myelin/arcflash/os_switcher_bootloader/display.cc

// Copyright 2019 Google LLC
//
// Licensed under the Apache License, Version 2.0 (the "License");
// you may not use this file except in compliance with the License.
// You may obtain a copy of the License at
//
//     http://www.apache.org/licenses/LICENSE-2.0
//
// Unless required by applicable law or agreed to in writing, software
// distributed under the License is distributed on an "AS IS" BASIS,
// WITHOUT WARRANTIES OR CONDITIONS OF ANY KIND, either express or implied.
// See the License for the specific language governing permissions and
// limitations under the License.

#include "arcflash.h"
#include <stdarg.h>

int display_x = 0, display_y = 0;

// riscosfont is defined in third_party/riscos/riscos_font.s
extern "C" {
	extern const uint8_t riscos_font[8 * 256];
}

void display_goto(int x, int y) {
	display_x = x;
	display_y = y;
}

static void newline() {
	display_x = 0;
	display_y += 8;
	if (display_y > HEIGHT - 1) {
		// copy entire page up 8 rows
		for (volatile uint32_t *ptr = (volatile uint32_t *)SCREEN;
			ptr < (volatile uint32_t *)SCREEN_ADDR(0, HEIGHT - 8);
			ptr++)
		{
			*ptr = *(volatile uint32_t *)((volatile uint8_t *)ptr + WIDTH * 8);
		}
		display_y -= 8;

		// clear bottom row
		for (volatile uint32_t *ptr = (volatile uint32_t *)SCREEN_ADDR(0, HEIGHT - 8);
			ptr < (volatile uint32_t *)SCREEN_ADDR(0, HEIGHT);
			ptr++)
		{
			*ptr = 0;
		}
	}
}

void display_print_char(char c) {
	switch (c) {
		case '\r':
			display_x = 0;
			return;
		case '\n':
			newline();
			return;
	}

	const uint8_t *patternptr = &riscos_font[8 * c];
	volatile uint8_t *displayptr = SCREEN + display_x + display_y * 640;
	for (int y = 0; y < 8; ++y) {
		uint8_t pattern = *patternptr++;
		for (int x = 0; x < 8; ++x) {
			SCREEN[(y + display_y) * WIDTH + (x + display_x)] = (pattern & 0x80) ? WHITE : BLACK;
			pattern <<= 1;
		}
		displayptr += 640 - 8;
	}
	display_x += 8;
	if (display_x >= WIDTH) {
		newline();
	}
}

void display_print(const char* s) {
	for (const uint8_t *sptr = (const uint8_t *)s; *sptr; sptr++) {
		display_print_char(*sptr);
	}
}

char hex_digit(int v) {
	if (v < 10)
		return '0' + v;
	if (v < 16)
		return 'A' + v - 10;
	return 'X';
}

void display_print_hex(uint32_t v) {
	char s[9];
	uint32_t digits = 1;
	while (digits < 8 && v > (1UL << (digits * 4))) {
		++digits;
	}
	uint32_t shift = (digits - 1) * 4;
	uint32_t mask = 15 << shift;
	for (uint32_t i = 0; i < digits; ++i) {
		s[i] = hex_digit((v & mask) >> shift);
		mask >>= 4;
		shift -= 4;
	}
	s[digits] = 0;
	display_print(s);
}
